TinyCircuits/TinyCircuits-TinyScreen_OLED-ASD2431/images/ASD2431-R-Tutorial-Image-01.jpg

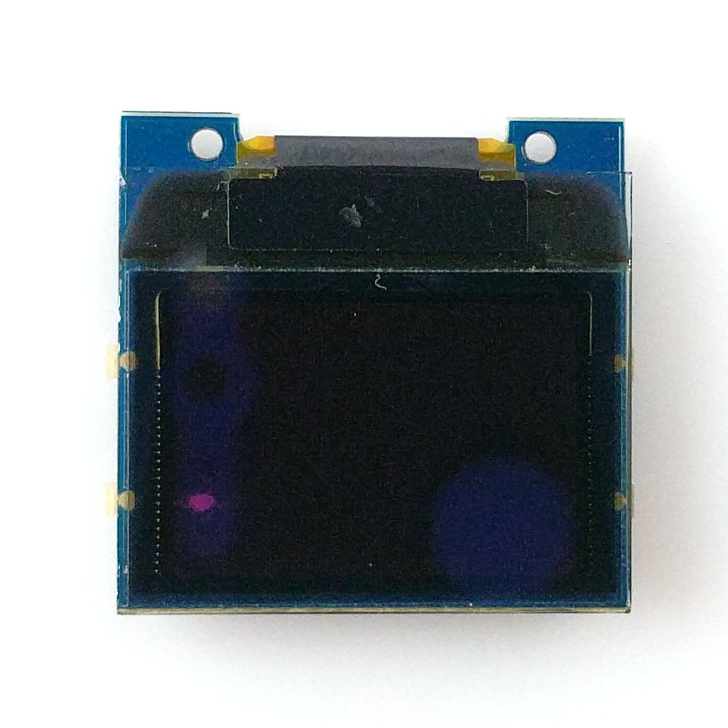
images/ASD2431-R-Tutorial-Image-01.jpg
