TinyCircuits/TinyCircuits-TinyScreen_OLED-ASD2431/images/ASD2431-R-Tutorial-Image-01.png

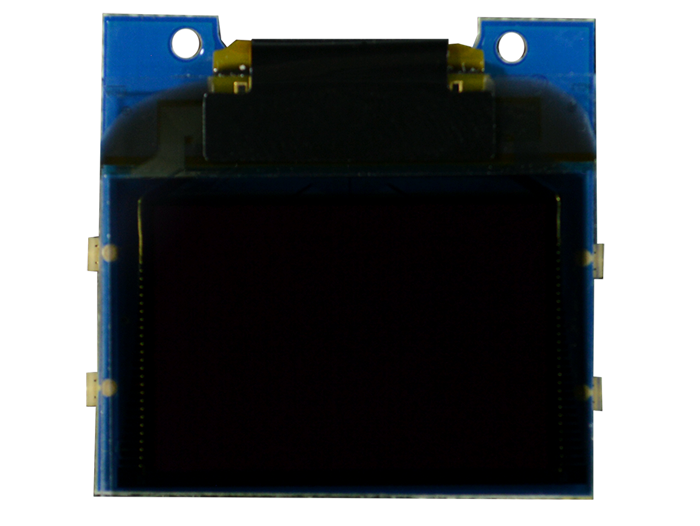
images/ASD2431-R-Tutorial-Image-01.png
